Thilos-Projects/Raumvermessungsroboter/Dokument/Bilder/Datenblätter/NemaDatenBlatt.jpg

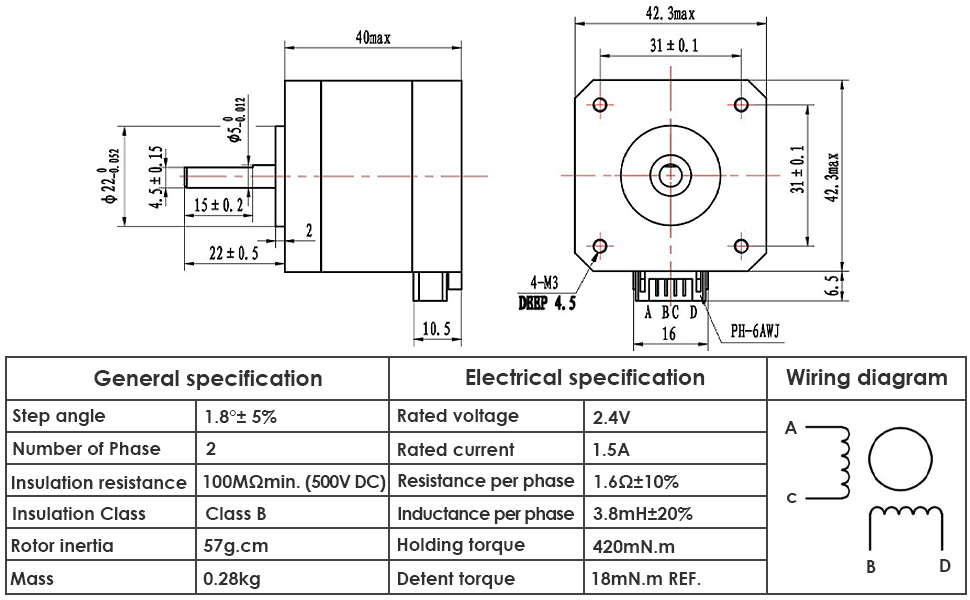
Dokument/Bilder/Datenblätter/NemaDatenBlatt.jpg
