Thilos-Projects/Raumvermessungsroboter/Dokument/Bilder/Fahrwerk/Fahrwerk.PNG

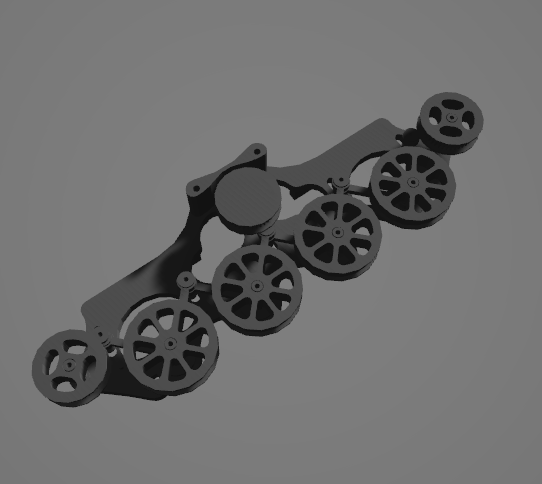
Dokument/Bilder/Fahrwerk/Fahrwerk.PNG
