Thilos-Projects/Raumvermessungsroboter/Dokument/Bilder/Fahrwerk/Fahrwerk_Grundplatte.PNG

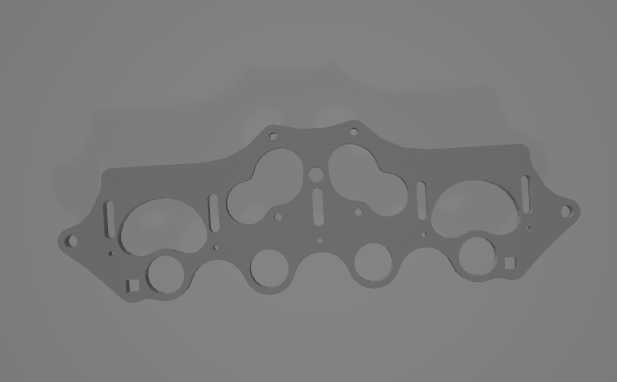
Dokument/Bilder/Fahrwerk/Fahrwerk_Grundplatte.PNG
