Thilos-Projects/Raumvermessungsroboter/Dokument/Bilder/Fahrwerk/FahrwerkRückplatte.png

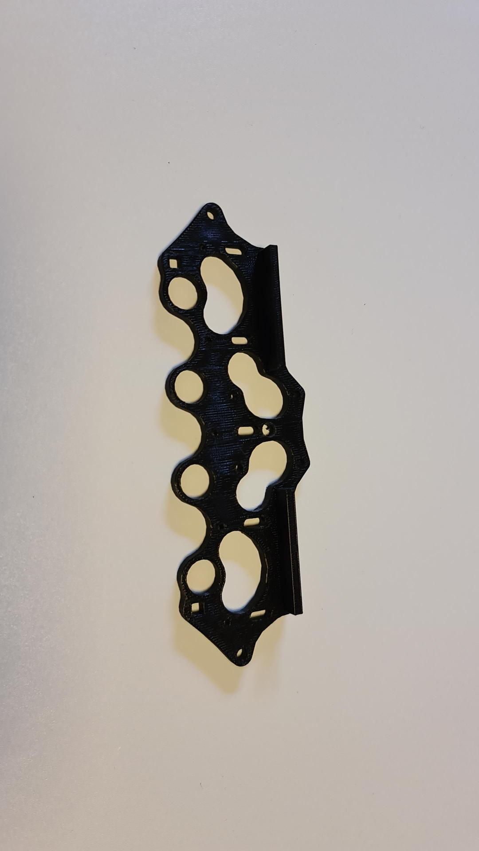
Dokument/Bilder/Fahrwerk/FahrwerkRückplatte.png
