Thilos-Projects/Raumvermessungsroboter/Dokument/Bilder/Fahrwerk/Fahrwert_Stand_3.5.21.png

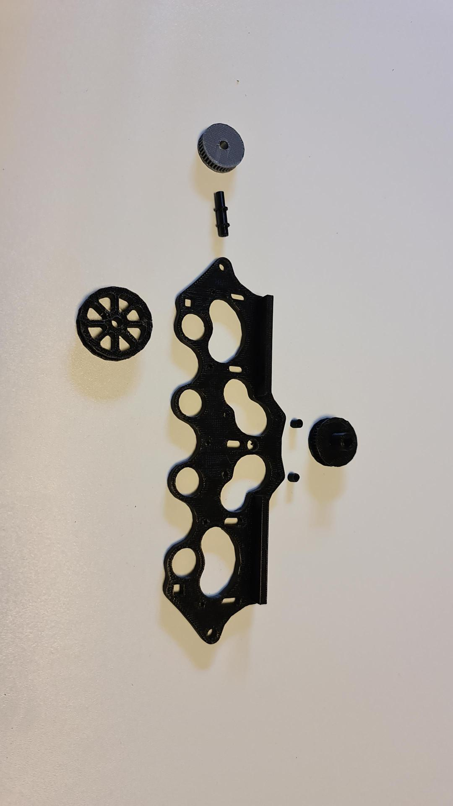
Dokument/Bilder/Fahrwerk/Fahrwert_Stand_3.5.21.png
