Thilos-Projects/Raumvermessungsroboter/Dokument/Bilder/Fahrwerk/Federung_Anker.PNG

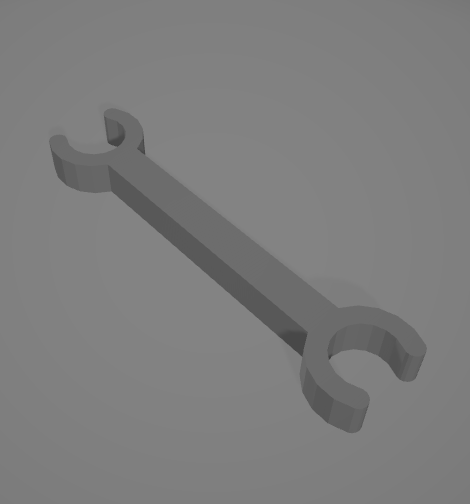
Dokument/Bilder/Fahrwerk/Federung_Anker.PNG
