Thilos-Projects/Raumvermessungsroboter/Dokument/Bilder/Fahrwerk/KettenHalterung.PNG

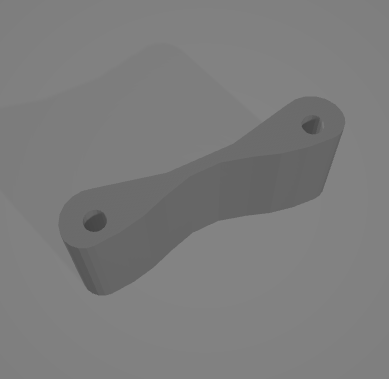
Dokument/Bilder/Fahrwerk/KettenHalterung.PNG
