Thilos-Projects/Raumvermessungsroboter/Dokument/Bilder/Fahrwerk/MotorZahnrad.PNG

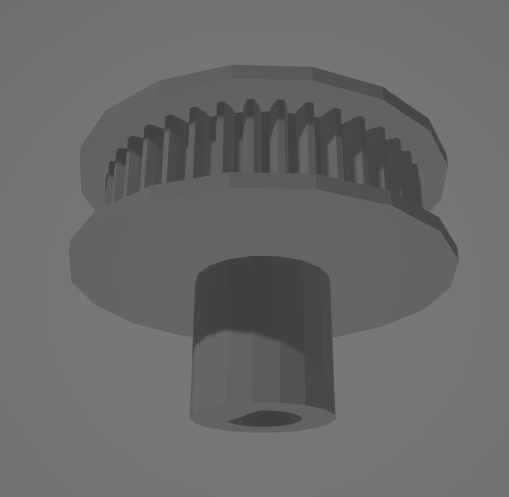
Dokument/Bilder/Fahrwerk/MotorZahnrad.PNG
