Thilos-Projects/Raumvermessungsroboter/Dokument/Bilder/Fahrwerk/Rad.PNG

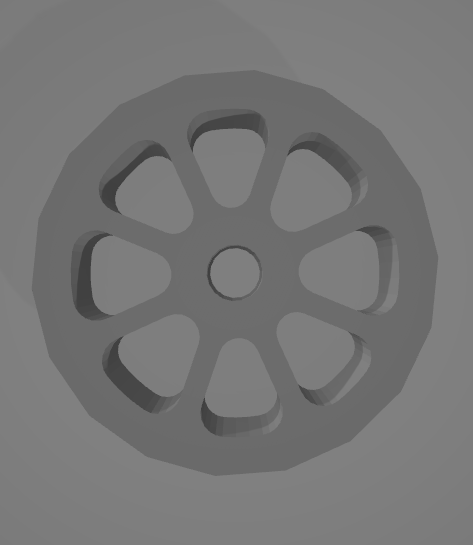
Dokument/Bilder/Fahrwerk/Rad.PNG
