Thilos-Projects/Raumvermessungsroboter/Dokument/Bilder/Fahrwerk/Rad_Achse.PNG

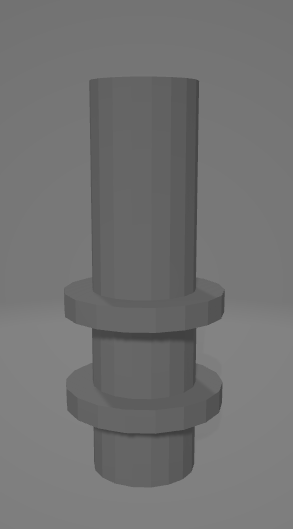
Dokument/Bilder/Fahrwerk/Rad_Achse.PNG
