Thilos-Projects/Raumvermessungsroboter/Dokument/Bilder/Fahrwerk/ZahnRad.PNG

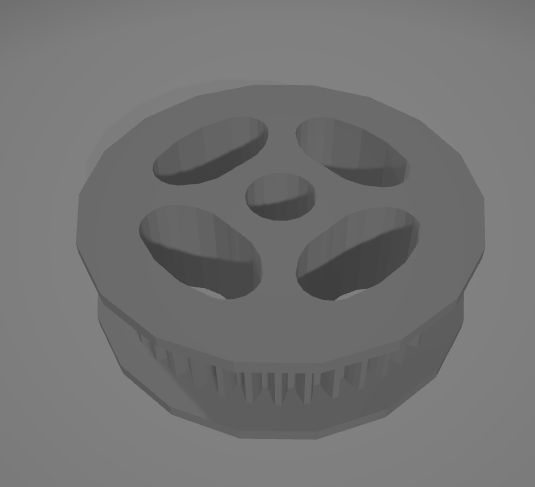
Dokument/Bilder/Fahrwerk/ZahnRad.PNG
