Thilos-Projects/Raumvermessungsroboter/Dokument/Bilder/Planung/LidarDrehtellerDarstellung_Plan.png

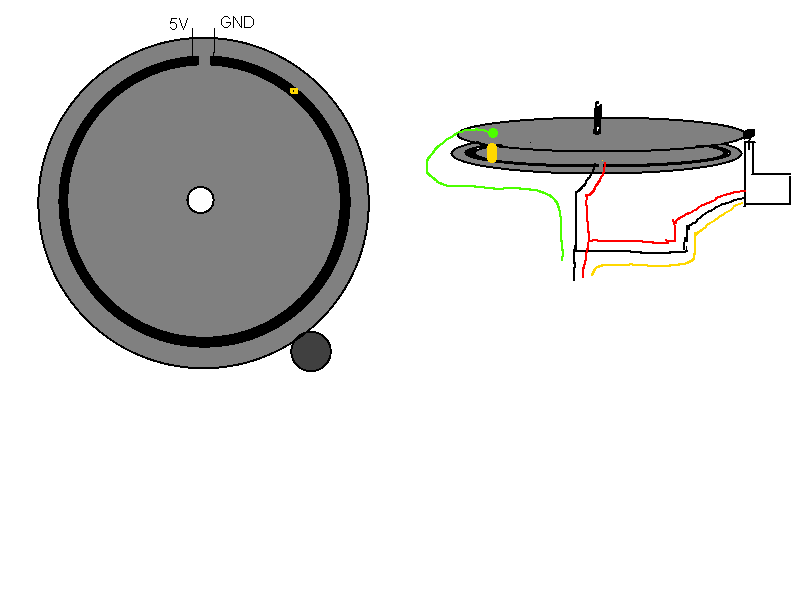
Dokument/Bilder/Planung/LidarDrehtellerDarstellung_Plan.png
