Thilos-Projects/Raumvermessungsroboter/Dokument/Bilder/Schritt2.png

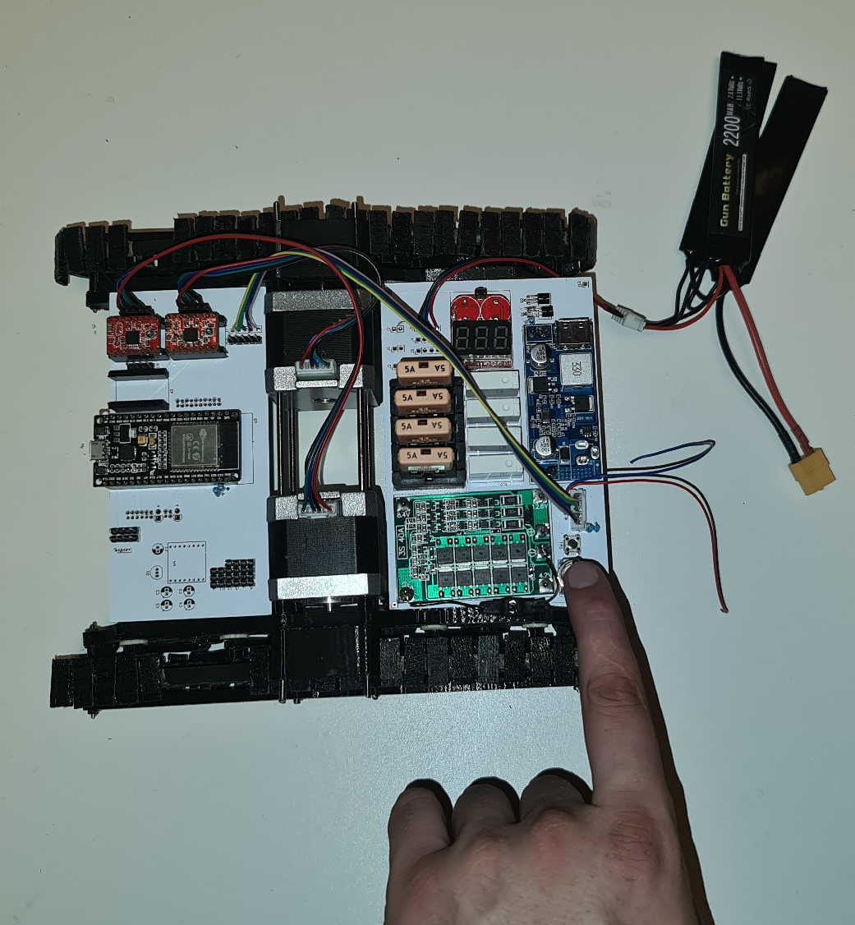
Dokument/Bilder/Schritt2.png
