Thilos-Projects/Raumvermessungsroboter/Dokument/Bilder/Schritt3.png

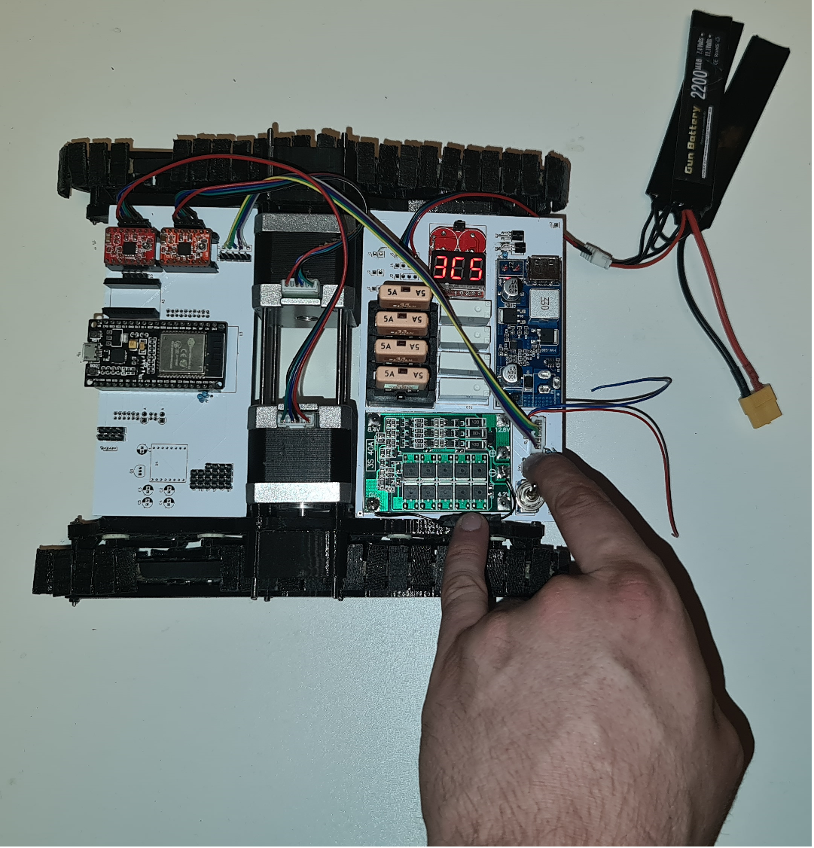
Dokument/Bilder/Schritt3.png
