Thilos-Projects/Raumvermessungsroboter/Dokument/Bilder/SpannungsVersorgung.png

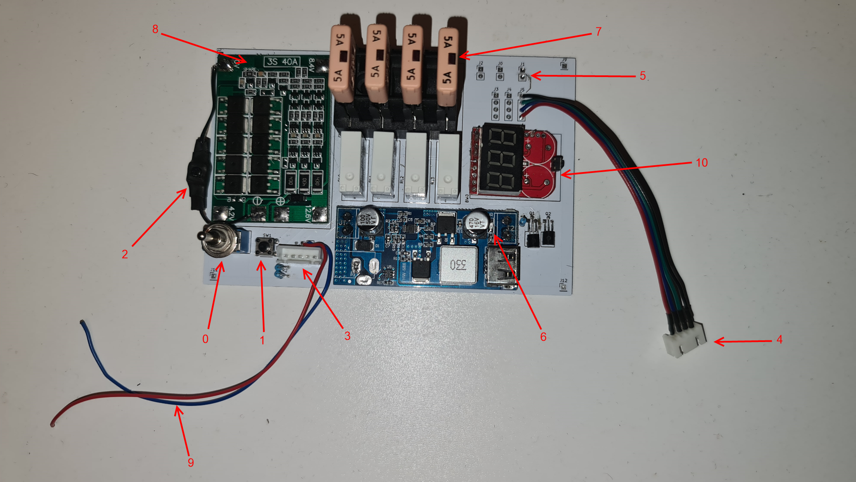
Dokument/Bilder/SpannungsVersorgung.png
