Thilos-Projects/Raumvermessungsroboter/3D_Komponenten/Fahrwerk/STLs/Fahrwerk_Federungs_Anker.stl

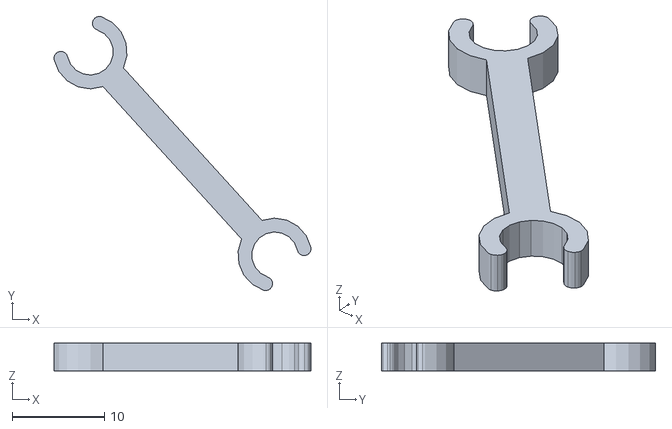
[picture p37: CAD file, 2021-05-07]
3D_Komponenten/Fahrwerk/STLs/Fahrwerk_Federungs_Anker.stl
27.8 x 29.7 x 3.00
