Thilos-Projects/Raumvermessungsroboter/3D_Komponenten/Fahrwerk/STLs/Fahrwerk_Federungs_abstandshalter.stl

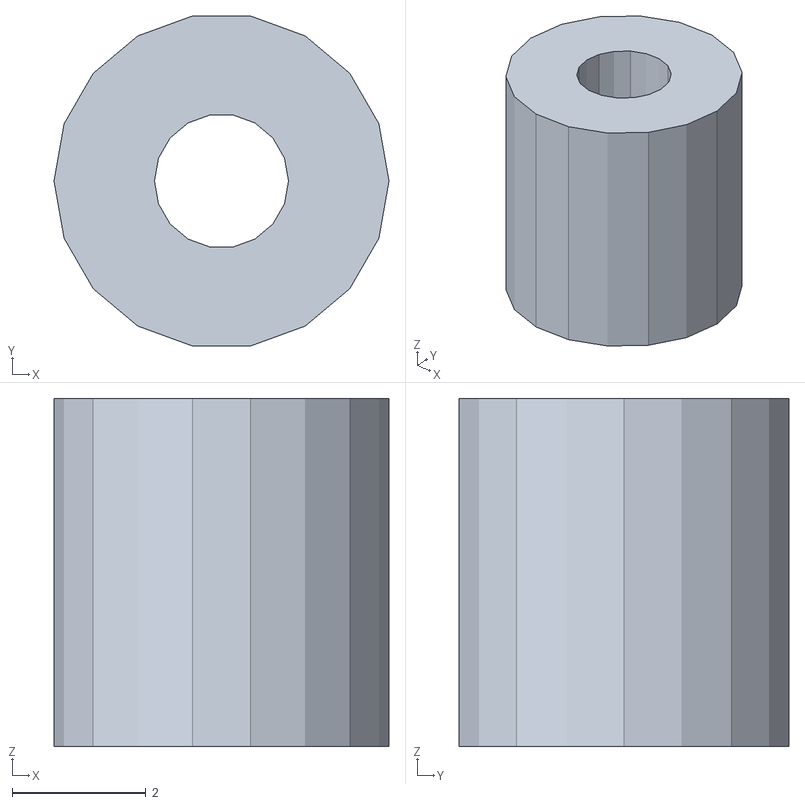
[picture p38: CAD file, 2021-05-07]
3D_Komponenten/Fahrwerk/STLs/Fahrwerk_Federungs_abstandshalter.stl
5.00 x 4.92 x 5.20
