Thilos-Projects/Raumvermessungsroboter/3D_Komponenten/Fahrwerk/STLs/Fahrwerk_Rad.stl

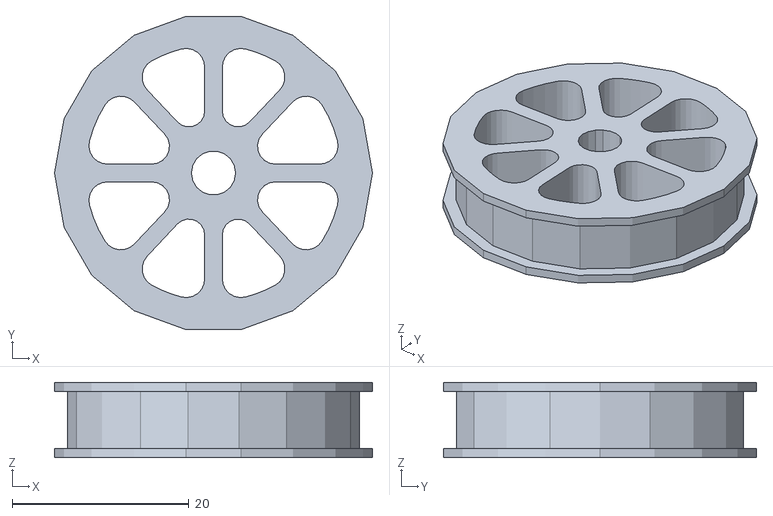
[picture p39: CAD file, 2021-05-07]
3D_Komponenten/Fahrwerk/STLs/Fahrwerk_Rad.stl
36.0 x 35.5 x 8.50
