Thilos-Projects/Raumvermessungsroboter/3D_Komponenten/Fahrwerk/STLs/Fahrwerk_Federungs_Gummi_Pine.stl

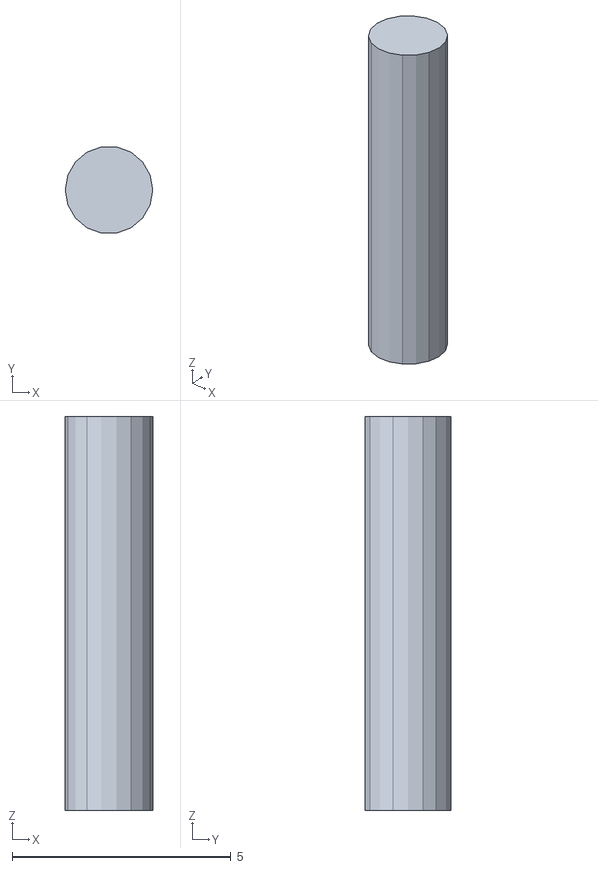
[picture p40: CAD file, 2021-05-07]
3D_Komponenten/Fahrwerk/STLs/Fahrwerk_Federungs_Gummi_Pine.stl
2.00 x 1.97 x 9.00
