Thilos-Projects/Raumvermessungsroboter/3D_Komponenten/Fahrwerk/STLs/Fahrwerk_Motor_Abstandshalter.stl

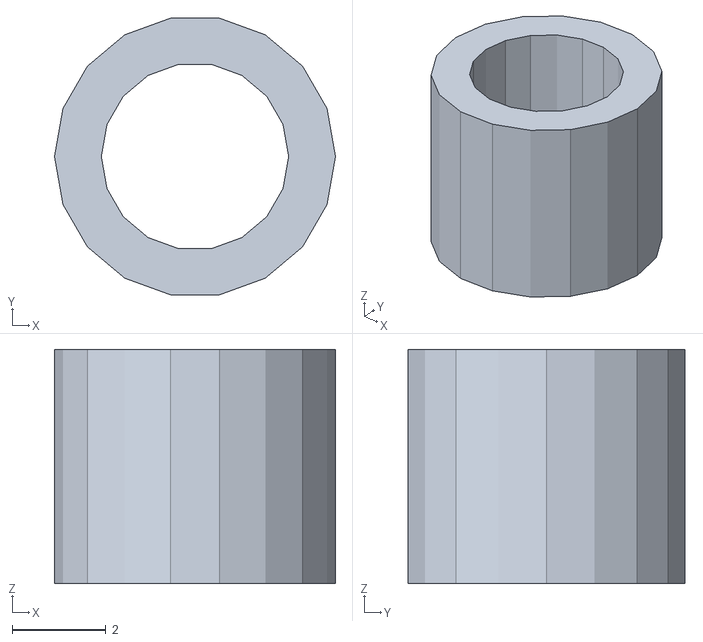
[picture p41: CAD file, 2021-05-07]
3D_Komponenten/Fahrwerk/STLs/Fahrwerk_Motor_Abstandshalter.stl
6.00 x 5.91 x 5.00
