Thilos-Projects/Raumvermessungsroboter/3D_Komponenten/Fahrwerk/STLs/Fahrwerk_Zahn_Rad.stl

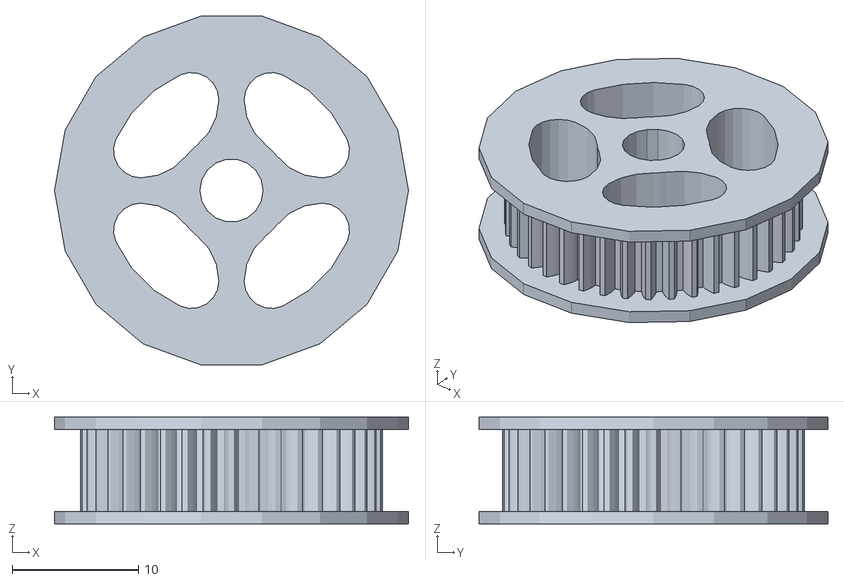
[picture p42: CAD file, 2021-05-07]
3D_Komponenten/Fahrwerk/STLs/Fahrwerk_Zahn_Rad.stl
28.0 x 27.6 x 8.45
